Tinkerforge/industrial-quad-relay-v2-bricklet/software/src/relay.c

/* industrial-quad-relay-v2-bricklet
 * Copyright (C) 2018 Olaf Lüke <olaf@tinkerforge.com>
 *
 * relay.c: Relay handling
 *
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
 * You should have received a copy of the GNU Lesser General Public
 * License along with this library; if not, write to the
 * Free Software Foundation, Inc., 59 Temple Place - Suite 330,
 * Boston, MA 02111-1307, USA.
 */

#include "relay.h"

#include "bricklib2/hal/system_timer/system_timer.h"

#include "xmc_gpio.h"

#include "configs/config_relay.h"

const uint8_t relay_pins[RELAY_NUM] = {RELAY0_PIN_NUM, RELAY1_PIN_NUM, RELAY2_PIN_NUM, RELAY3_PIN_NUM};
XMC_GPIO_PORT_t *relay_ports[RELAY_NUM] = {RELAY0_PORT, RELAY1_PORT, RELAY2_PORT, RELAY3_PORT};

Relay relay;

bool relay_get(const uint8_t pin) {
	return !XMC_GPIO_GetInput(relay_ports[pin], relay_pins[pin]);
}

void relay_set(const uint8_t pin, const bool value) {
	XMC_GPIO_SetOutputLevel(relay_ports[pin], relay_pins[pin], value ? XMC_GPIO_OUTPUT_LEVEL_LOW : XMC_GPIO_OUTPUT_LEVEL_HIGH);
}

void relay_init(void) {
	memset(&relay, 0, sizeof(Relay));

	XMC_GPIO_CONFIG_t button_pin_config = {
		.mode         = XMC_GPIO_MODE_OUTPUT_PUSH_PULL,
		.output_level = XMC_GPIO_OUTPUT_LEVEL_HIGH,
	};

	for(uint8_t i = 0; i < RELAY_NUM; i++) {
		XMC_GPIO_Init(relay_ports[i], relay_pins[i], &button_pin_config);
		relay.monoflop_done[i] = true;

		// Init channel LEDs
		relay.channel_leds[i].port_base = (XMC_GPIO_PORT_t *)PORT0_BASE;

		if(i == 0) {
			relay.channel_leds[i].pin = 12;
		}
		else if(i == 1) {
			relay.channel_leds[i].pin = 9;
		}
		else if(i == 2) {
			relay.channel_leds[i].pin = 8;
		}
		else if(i == 3) {
			relay.channel_leds[i].pin = 7;
		}

		button_pin_config.output_level = XMC_GPIO_OUTPUT_LEVEL_HIGH;
		XMC_GPIO_Init(relay.channel_leds[i].port_base, relay.channel_leds[i].pin, &button_pin_config);

		relay.channel_leds[i].channel_led_flicker_state.config = LED_FLICKER_CONFIG_OFF;
		relay.channel_leds[i].config = INDUSTRIAL_QUAD_RELAY_V2_CHANNEL_LED_CONFIG_SHOW_CHANNEL_STATUS;
	}
}

void relay_tick(void) {
	for(uint8_t i = 0; i < RELAY_NUM; i++) {
		if(!relay.monoflop_done[i]) {
			if(system_timer_is_time_elapsed_ms(relay.monoflop_time_start[i], relay.monoflop_time[i])) {
				relay_set(i, !relay_get(i));
				relay.monoflop_callback[i] = true;
				relay.monoflop_done[i]     = true;
			}
		}

		// Manage channel LEDs
		switch (relay.channel_leds[i].config) {
			case INDUSTRIAL_QUAD_RELAY_V2_CHANNEL_LED_CONFIG_OFF:
				relay.channel_leds[i].channel_led_flicker_state.config = LED_FLICKER_CONFIG_OFF;
				XMC_GPIO_SetOutputHigh(relay.channel_leds[i].port_base, relay.channel_leds[i].pin); // Channel LED off

				break;

			case INDUSTRIAL_QUAD_RELAY_V2_CHANNEL_LED_CONFIG_ON:
				relay.channel_leds[i].channel_led_flicker_state.config = LED_FLICKER_CONFIG_ON;
				XMC_GPIO_SetOutputLow(relay.channel_leds[i].port_base, relay.channel_leds[i].pin); // Channel LED on

				break;

			case INDUSTRIAL_QUAD_RELAY_V2_CHANNEL_LED_CONFIG_SHOW_HEARTBEAT:
				relay.channel_leds[i].channel_led_flicker_state.config = LED_FLICKER_CONFIG_HEARTBEAT;

				led_flicker_tick(&relay.channel_leds[i].channel_led_flicker_state,
				                 system_timer_get_ms(),
				                 relay.channel_leds[i].port_base,
				                 relay.channel_leds[i].pin);

				break;

			case INDUSTRIAL_QUAD_RELAY_V2_CHANNEL_LED_CONFIG_SHOW_CHANNEL_STATUS:
				relay.channel_leds[i].channel_led_flicker_state.config = LED_FLICKER_CONFIG_OFF;

				if(relay_get(i)) {
					// Input channel has logic high
					XMC_GPIO_SetOutputLow(relay.channel_leds[i].port_base, relay.channel_leds[i].pin); // Channel LED on
				}
				else {
					// Input channel has logic low
					XMC_GPIO_SetOutputHigh(relay.channel_leds[i].port_base, relay.channel_leds[i].pin); // Channel LED off
				}

				break;

			default:
				break;
		}
	}
}
